stefanofinetti/MF_fcu_efis_mainboard/STL Files/PushPullBlackFlipper.stl

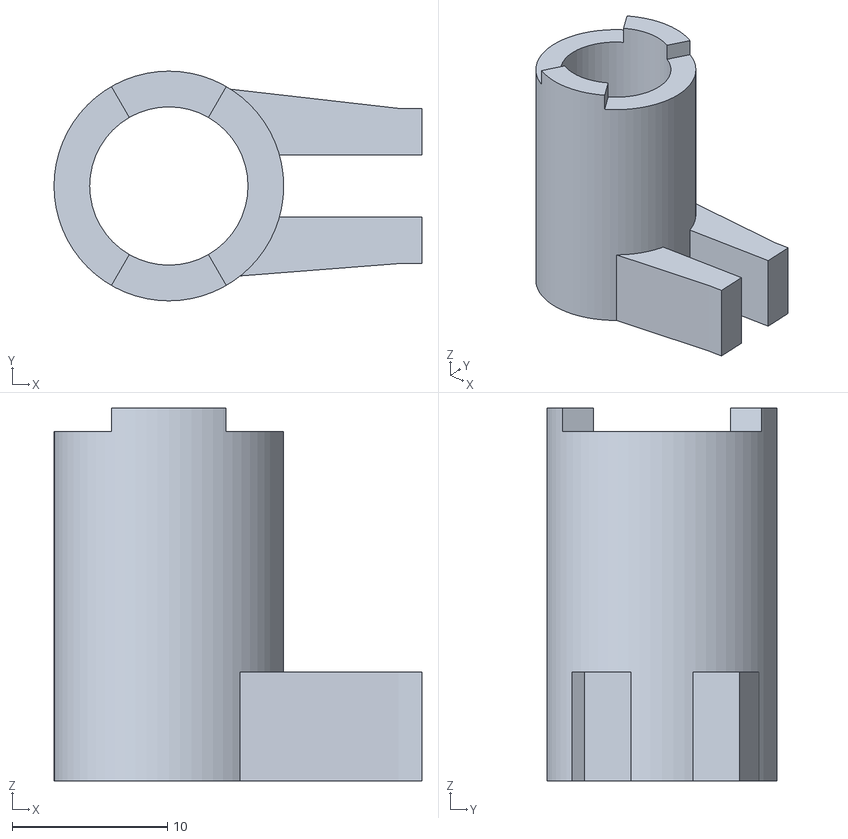
[picture p17: CAD file, 2026-09-20]
STL Files/PushPullBlackFlipper.stl
23.7 x 14.8 x 24.0
