stefanofinetti/MF_fcu_efis_mainboard/STL Files/Rotaries/VSpeedKnob_Base.stl

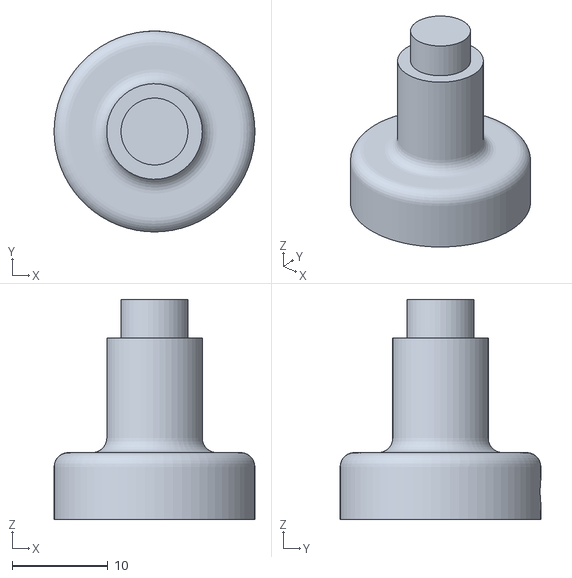
[picture p18: CAD file, 2026-09-20]
STL Files/Rotaries/VSpeedKnob_Base.stl
21.0 x 21.0 x 23.0
