stefanofinetti/MF_fcu_efis_mainboard/STL Files/V4C/FCU_LEFT.3mf

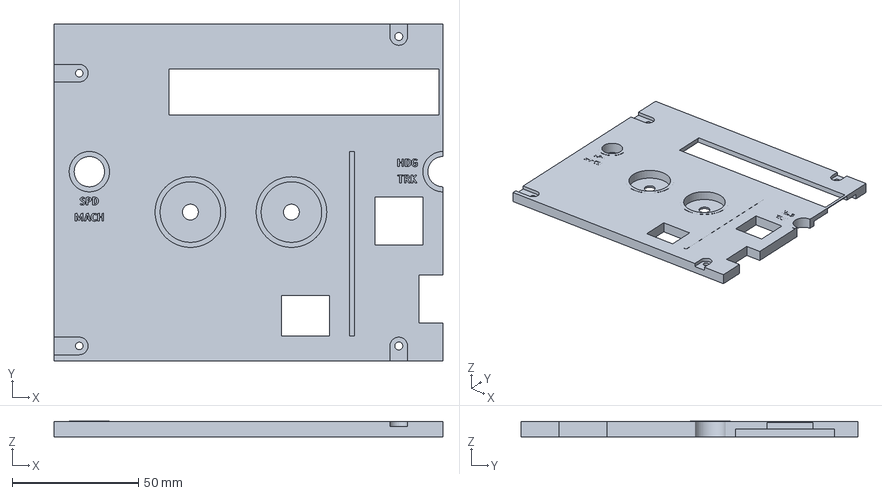
[picture p19: CAD file, 2025-02-01]
STL Files/V4C/FCU_LEFT.3mf
154.0 x 133.5 x 6.18 mm
