stefanofinetti/MF_fcu_efis_mainboard/PSU/3dmodels/Fuse_Bourns_MF-RHT200.step

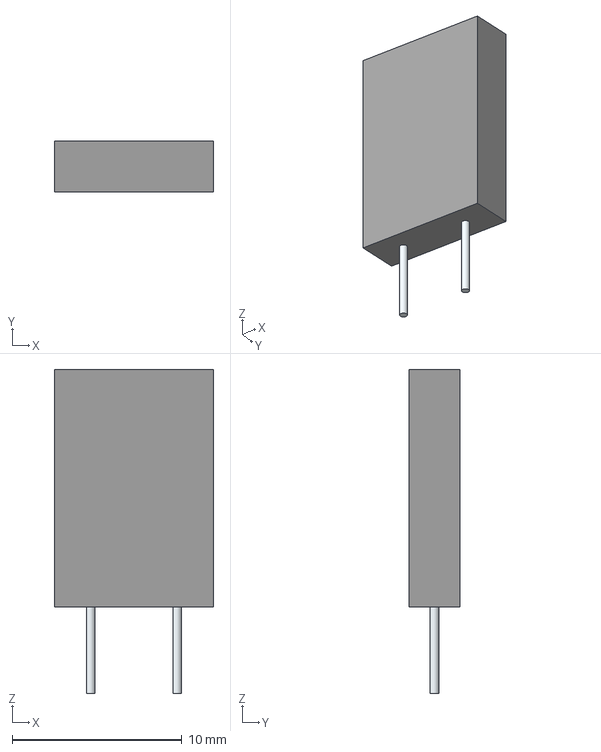
[picture p20: CAD file, 2026-09-22]
PSU/3dmodels/Fuse_Bourns_MF-RHT200.step
9.40 x 3.00 x 19.1 mm
Leads
