stefanofinetti/MF_fcu_efis_mainboard/STL Files/Black/EFIS_FRAME_RIGHT.stl

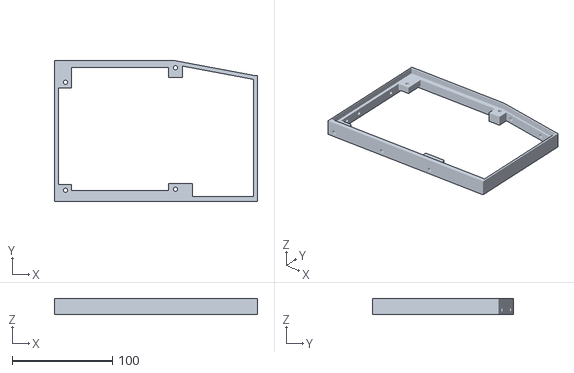
[picture p21: CAD file, 2026-09-20]
STL Files/Black/EFIS_FRAME_RIGHT.stl
203.0 x 140.5 x 16.0
