stefanofinetti/MF_fcu_efis_mainboard/STL Files/FCU_UNIT_V5.3mf

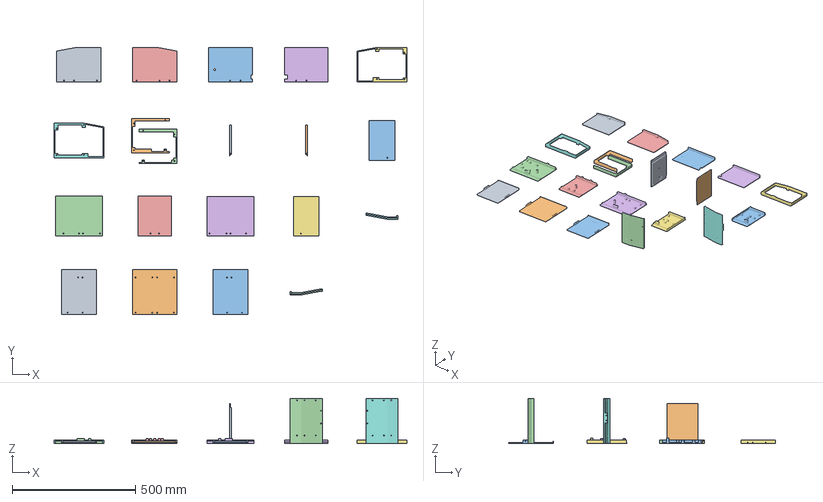
[picture p22: CAD file, 2026-09-20]
STL Files/FCU_UNIT_V5.3mf
1430.8 x 1083.8 x 184.0 mm
EFIS_BACK_LEFT.stl
FCU_FRAME_LEFT.stl
FCU_BACK_LEFT.stl
FCU_FRAME_RIGHT.stl
EFIS_BACK_RIGHT.stl
FCU_BACK_RIGHT.stl
EFIS_FRAME_LEFT.stl
EFIS_FRAME_RIGHT.stl
UNIT_LEFT.stl
UNIT_RIGHT.stl
UNIT_BOTTOM_LEFT.stl
UNIT_BOTTOM_CENTER_LEFT.stl
UNIT_BOTTOM_CENTER.stl
UNIT_BOTTOM_CENTER_RIGHT.stl
UNIT_BOTTOM_RIGHT.stl
UNIT_TOP_LEFT.stl
UNIT_TOP_CENTER_LEFT.stl
UNIT_TOP_CENTER.stl
UNIT_TOP_CENTER_RIGHT.stl
UNIT_TOP_RIGHT.stl
