stefanofinetti/MF_fcu_efis_mainboard/STL Files/Korry_19x16/Korry19_16_project_V5.3mf

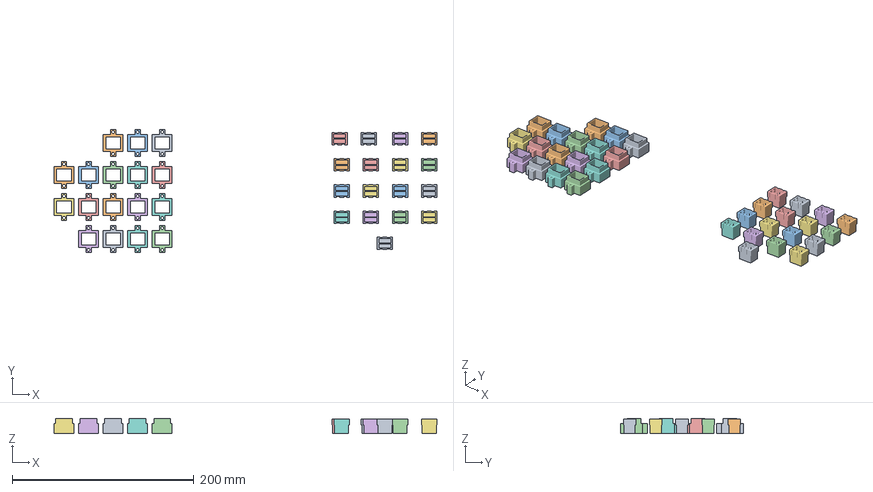
[picture p23: CAD file, 2025-06-19]
STL Files/Korry_19x16/Korry19_16_project_V5.3mf
421.2 x 135.8 x 17.0 mm
Korry19x16_case_v5.stl x 17
APPR_BLACK
ARPT_BLACK x 2
FD_BLACK x 2
CSTR_BLACK x 2
LS_BLACK x 2
NDB_BLACK x 2
VORD_BLACK x 2
WPT_BLACK x 2
EXPD_BLACK
LOC_BLACK
