stefanofinetti/MF_fcu_efis_mainboard/STL Files/Korry_19x19/AT_button.stl

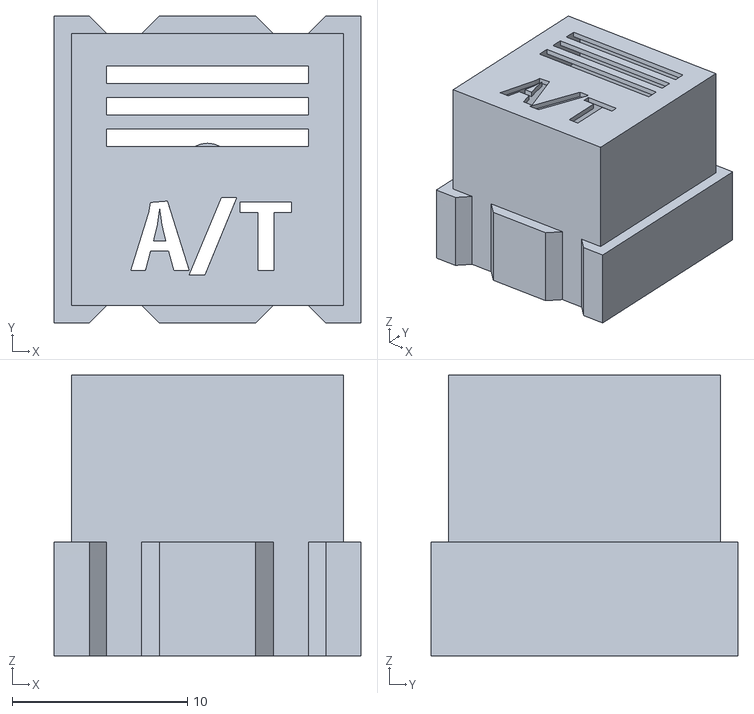
[picture p25: CAD file, 2026-09-20]
STL Files/Korry_19x19/AT_button.stl
17.5 x 17.5 x 16.0
