stefanofinetti/MF_fcu_efis_mainboard/STL Files/Rotaries/PushPull_VSPD_SPD_HDG_case.3mf

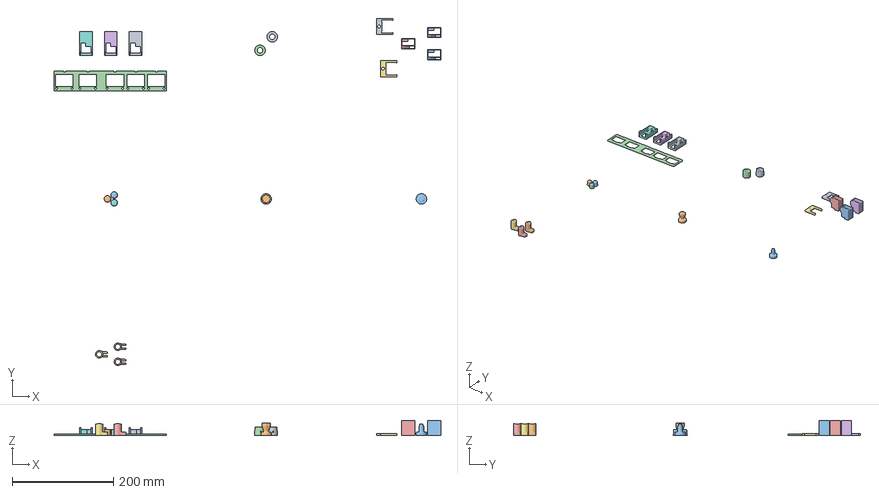
[picture p26: CAD file, 2026-09-20]
STL Files/Rotaries/PushPull_VSPD_SPD_HDG_case.3mf
765.2 x 686.4 x 30.0 mm
PushPullBlackSelector.stl x 2
PushPullBlackFlipper.stl x 3
FCU_BlackButtons_Button x 3
PushPull_ALT_SPD_HDG_cables_case.stl x 3
PushPull_ALT_SPD_HDG_mech_case.stl x 3
FCU_V4_OLED_MASK_V4.stl
PushPullBlackSwitchHolder.stl x 2
HeadingKnob.stl
VSpeedKnob_Base.stl
