stefanofinetti/MF_fcu_efis_mainboard/STL Files/FCU_BlackButtons_TransparentBase.stl

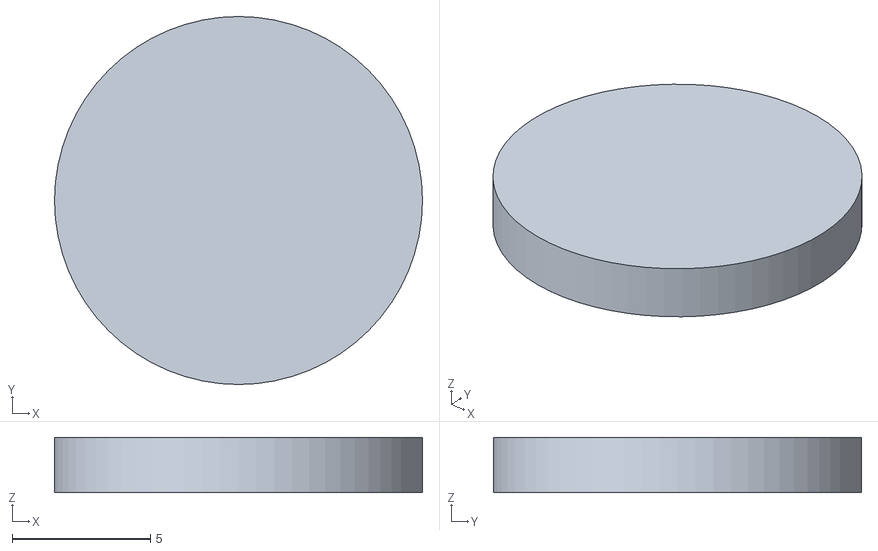
[picture p27: CAD file, 2025-06-21]
STL Files/FCU_BlackButtons_TransparentBase.stl
13.3 x 13.3 x 2.00
