stefanofinetti/MF_fcu_efis_mainboard/STL Files/Korry_19x16/TEST_REVERSED_NDB.stl

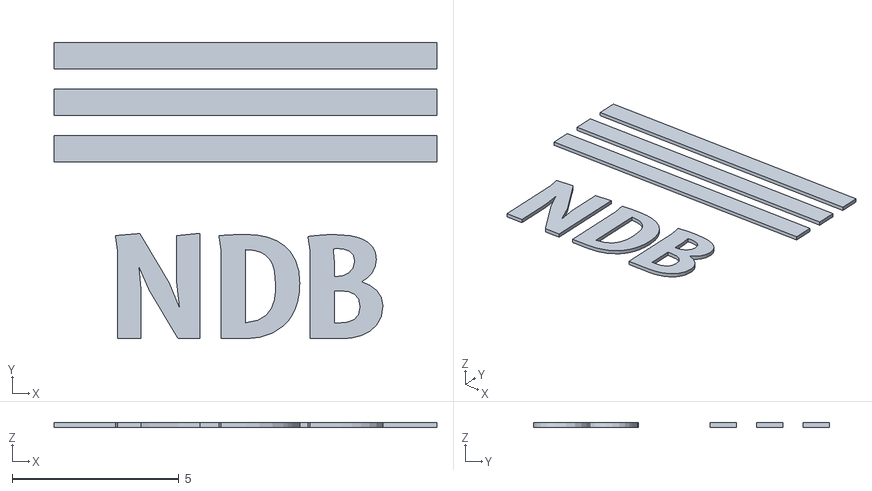
[picture p28: CAD file, 2025-06-19]
STL Files/Korry_19x16/TEST_REVERSED_NDB.stl
11.5 x 8.90 x 0.14
