stefanofinetti/MF_fcu_efis_mainboard/STL Files/Rotaries/PushPullBlackSelector.3mf

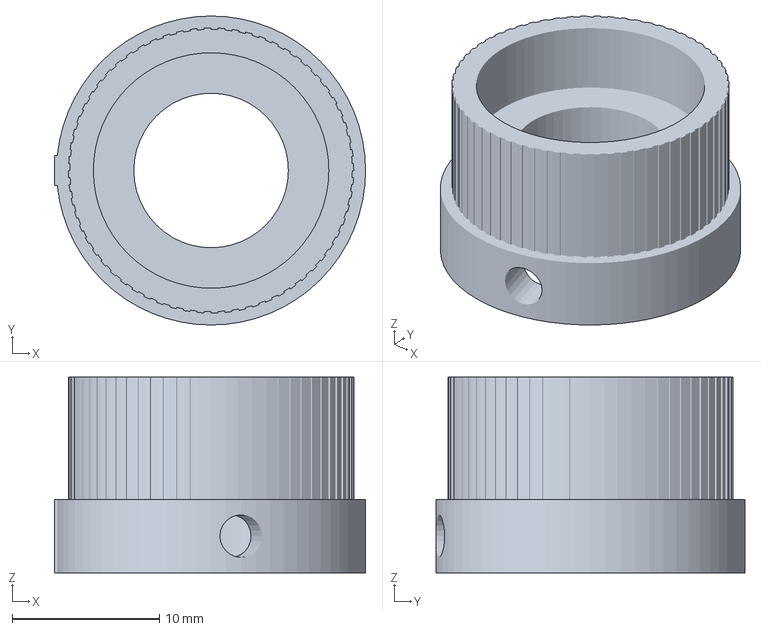
[picture p30: CAD file, 2026-09-20]
STL Files/Rotaries/PushPullBlackSelector.3mf
21.1 x 21.0 x 13.3 mm
