stefanofinetti/MF_fcu_efis_mainboard/STL Files/V4C/FCU_LEFT_TRASP.stl

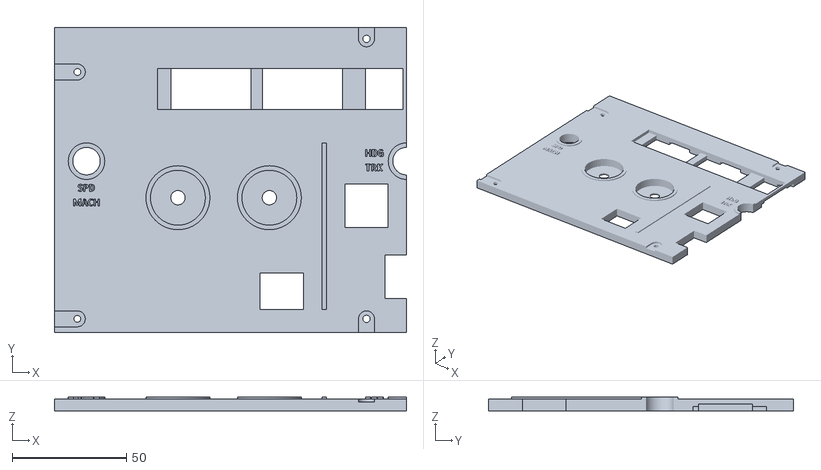
[picture p31: CAD file, 2025-02-01]
STL Files/V4C/FCU_LEFT_TRASP.stl
154.0 x 133.5 x 6.04
