stefanofinetti/MF_fcu_efis_mainboard/STL Files/01_EFIS_V4b_LEFT_firstlayer_transparent.stl

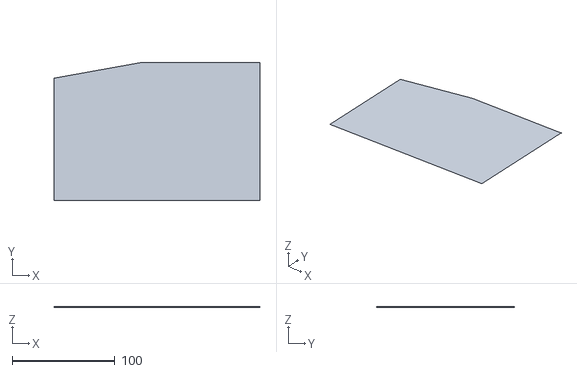
[picture p32: CAD file, 2025-06-21]
STL Files/01_EFIS_V4b_LEFT_firstlayer_transparent.stl
200.0 x 133.5 x 0.1
