stefanofinetti/MF_fcu_efis_mainboard/STL Files/Black/EFIS_BACK_LEFT.stl

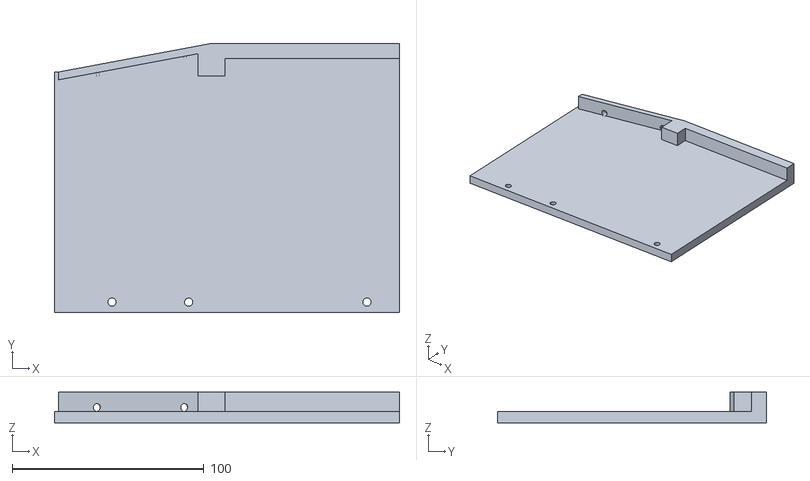
[picture p33: CAD file, 2025-06-19]
STL Files/Black/EFIS_BACK_LEFT.stl
180.0 x 140.5 x 16.0
