stefanofinetti/MF_fcu_efis_mainboard/STL Files/Rotaries/HeadingKnob.stl

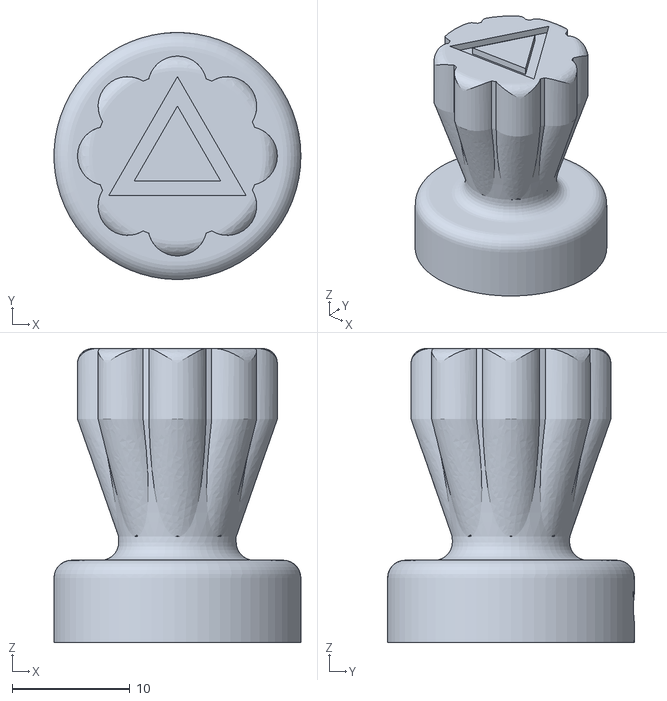
[picture p35: CAD file, 2026-09-20]
STL Files/Rotaries/HeadingKnob.stl
21.0 x 21.0 x 25.0
