stefanofinetti/MF_fcu_efis_mainboard/STL Files/V4C/FCU_RIGHT_GREY.stl

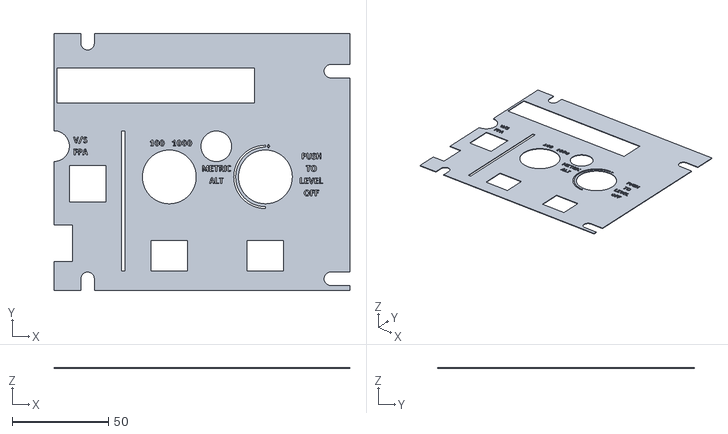
[picture p36: CAD file, 2025-02-01]
STL Files/V4C/FCU_RIGHT_GREY.stl
154.0 x 133.5 x 0.437
