stefanofinetti/MF_fcu_efis_mainboard/STL Files/Black/UNIT_TOP_CENTER_LEFT.stl

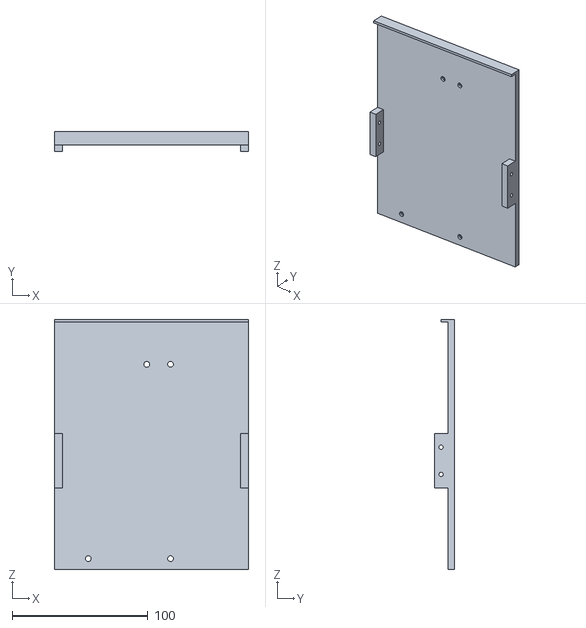
[picture p37: CAD file, 2025-06-19]
STL Files/Black/UNIT_TOP_CENTER_LEFT.stl
143.0 x 15.0 x 184.0
