stefanofinetti/MF_fcu_efis_mainboard/STL Files/FCU_BlackButtons_Button.stl

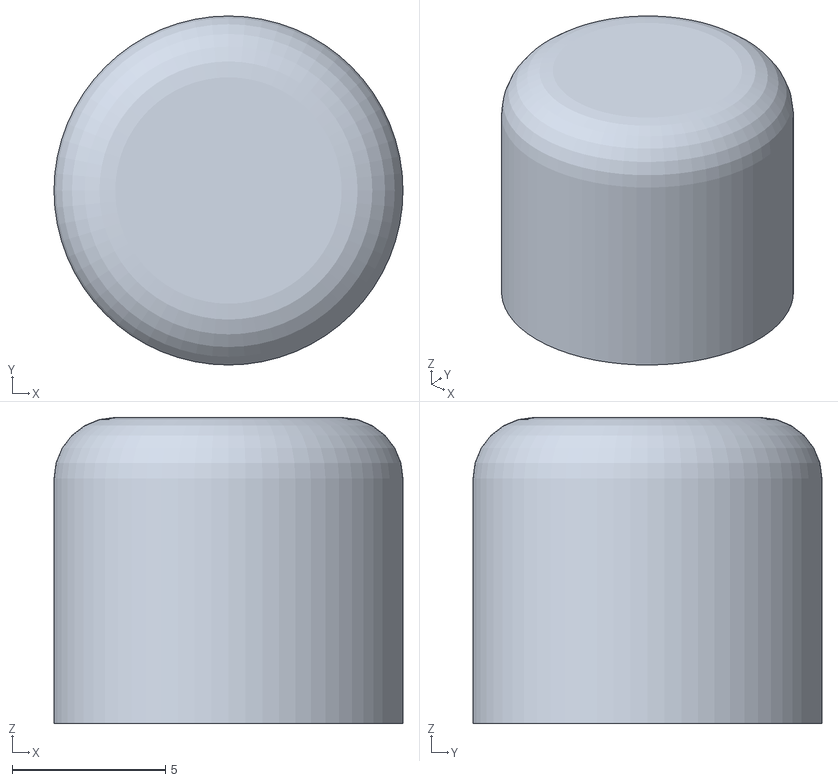
[picture p38: CAD file, 2025-06-21]
STL Files/FCU_BlackButtons_Button.stl
11.4 x 11.4 x 10.0
