stefanofinetti/MF_fcu_efis_mainboard/STL Files/Korry_19x16/V5/WPT_TRASP.stl

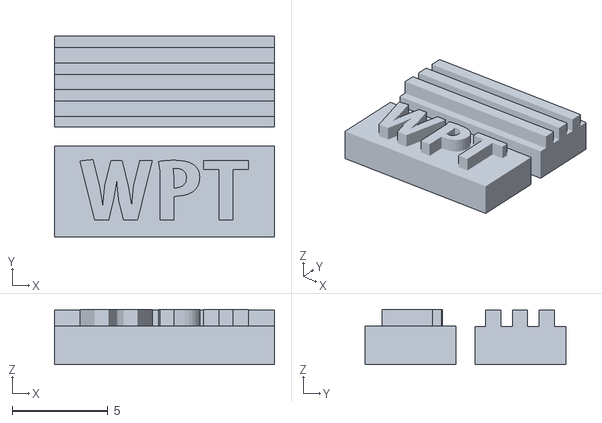
[picture p39: CAD file, 2025-06-19]
STL Files/Korry_19x16/V5/WPT_TRASP.stl
11.5 x 10.5 x 2.88
