stefanofinetti/MF_fcu_efis_mainboard/STL Files/Korry_19x19/AT_transparent.stl

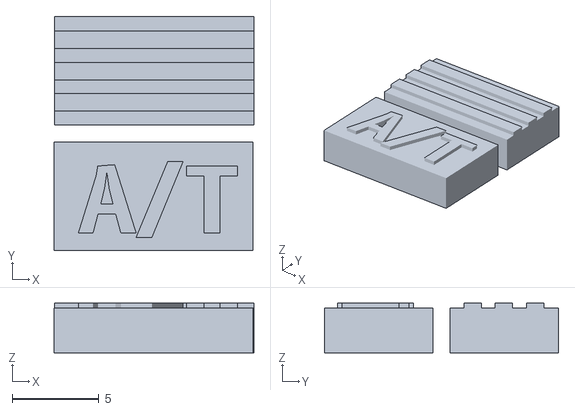
[picture p40: CAD file, 2025-06-21]
STL Files/Korry_19x19/AT_transparent.stl
11.5 x 13.5 x 2.86
