stefanofinetti/MF_fcu_efis_mainboard/STL Files/Rotaries/Rotary_ALT_BARO_Outer_case.stl

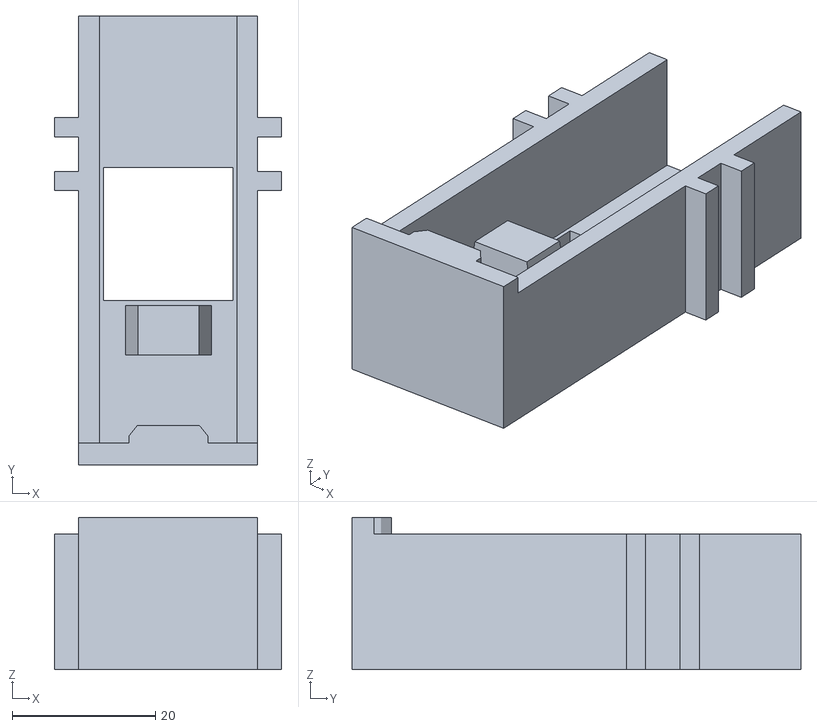
[picture p41: CAD file, 2026-09-20]
STL Files/Rotaries/Rotary_ALT_BARO_Outer_case.stl
31.7 x 62.6 x 21.2
