stefanofinetti/MF_fcu_efis_mainboard/STL Files/Korry_19x16/LS_white.stl

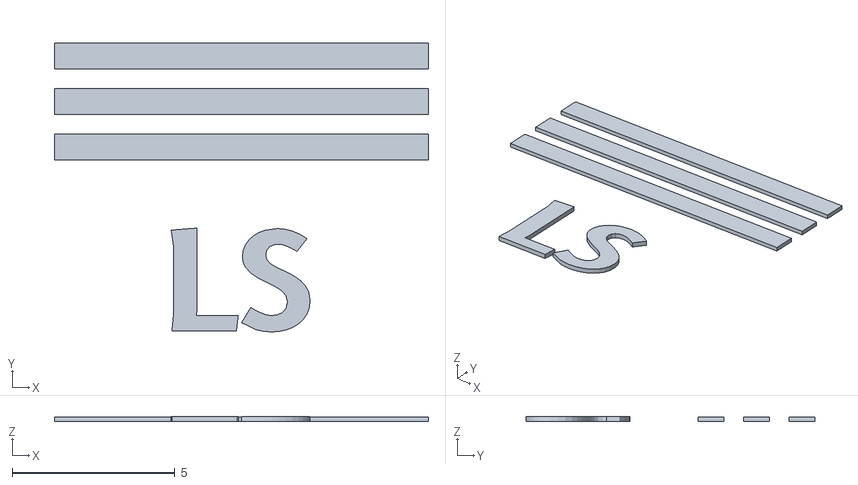
[picture p42: CAD file, 2024-11-27]
STL Files/Korry_19x16/LS_white.stl
11.5 x 8.88 x 0.16
