stefanofinetti/MF_fcu_efis_mainboard/STL Files/Rotaries/PushPull_VSPD_SPD_HDG_cables_case.stl

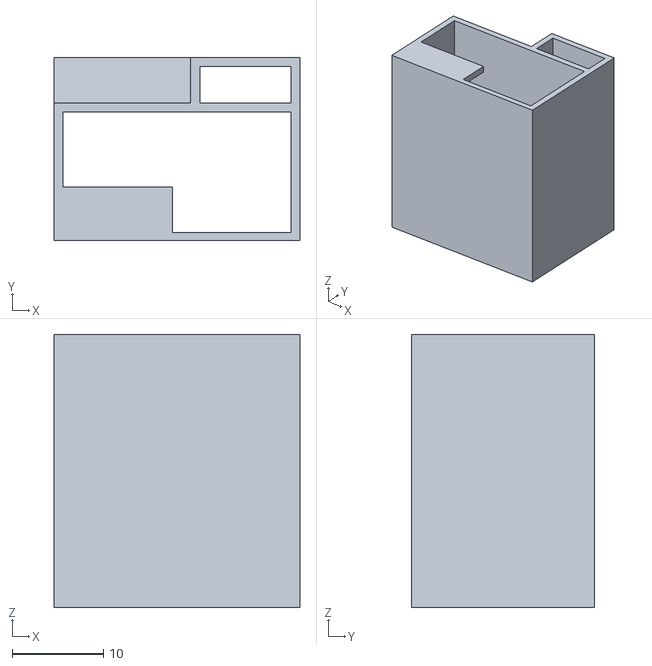
[picture p44: CAD file, 2025-06-19]
STL Files/Rotaries/PushPull_VSPD_SPD_HDG_cables_case.stl
27.0 x 20.1 x 30.0
