stefanofinetti/MF_fcu_efis_mainboard/STL Files/EVIS_V4b_Backlighting_Support.stl

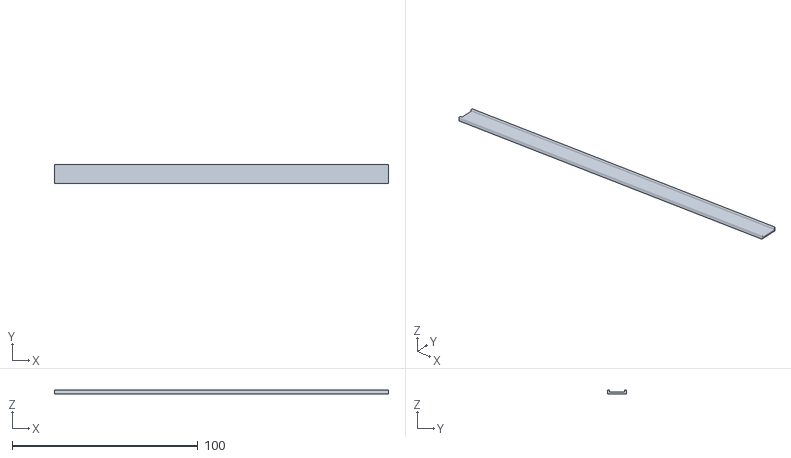
[picture p45: CAD file, 2025-06-19]
STL Files/EVIS_V4b_Backlighting_Support.stl
180.0 x 10.0 x 2.00
