stefanofinetti/MF_fcu_efis_mainboard/STL Files/Korry_19x19/AP2_white.stl

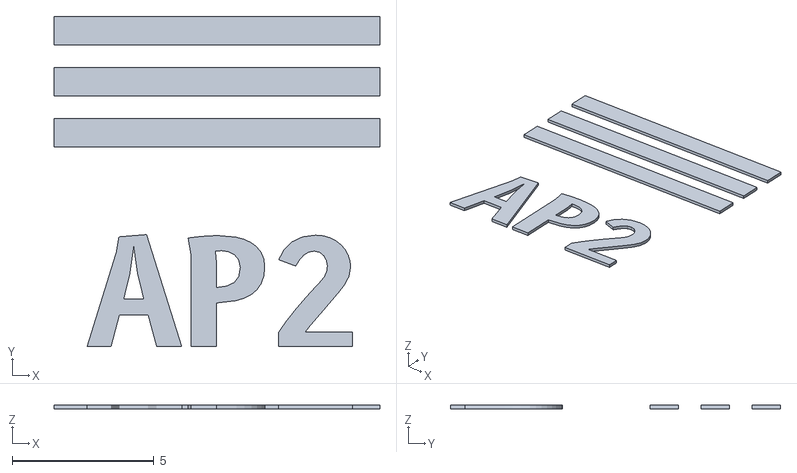
[picture p47: CAD file, 2025-06-21]
STL Files/Korry_19x19/AP2_white.stl
11.5 x 11.7 x 0.14
