stefanofinetti/MF_fcu_efis_mainboard/STL Files/Rotaries/PushPullBlackSwitchHolder.stl

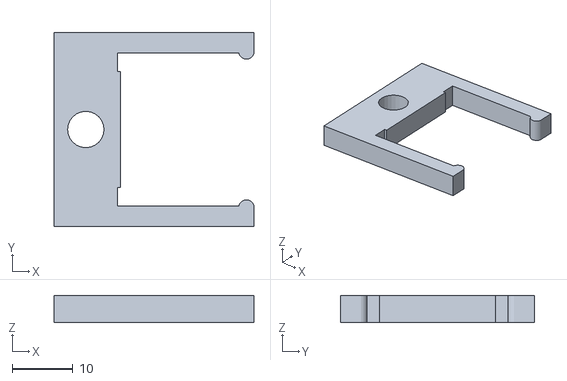
[picture p48: CAD file, 2025-06-19]
STL Files/Rotaries/PushPullBlackSwitchHolder.stl
33.0 x 32.0 x 4.50
