stefanofinetti/MF_fcu_efis_mainboard/STL Files/V4C/FCU_RIGHT_WHITE.stl

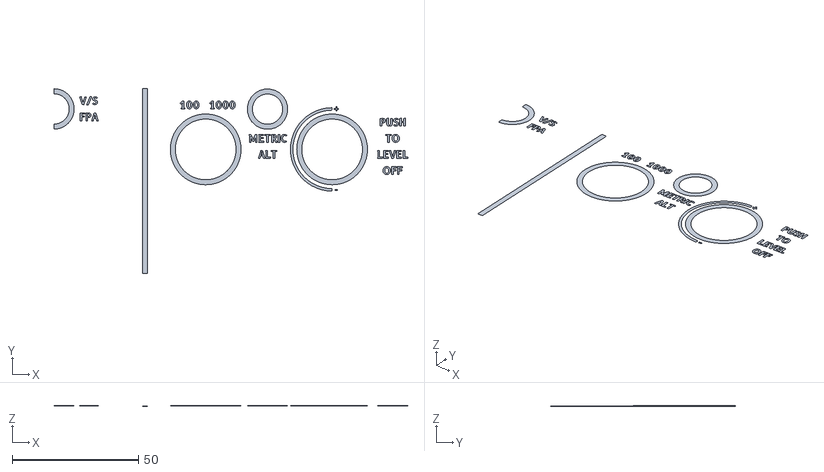
[picture p49: CAD file, 2025-02-01]
STL Files/V4C/FCU_RIGHT_WHITE.stl
140.0 x 73.0 x 0.22
