stefanofinetti/MF_fcu_efis_mainboard/STL Files/05_FCU_V4b_RIGHT_RAILS_white.stl

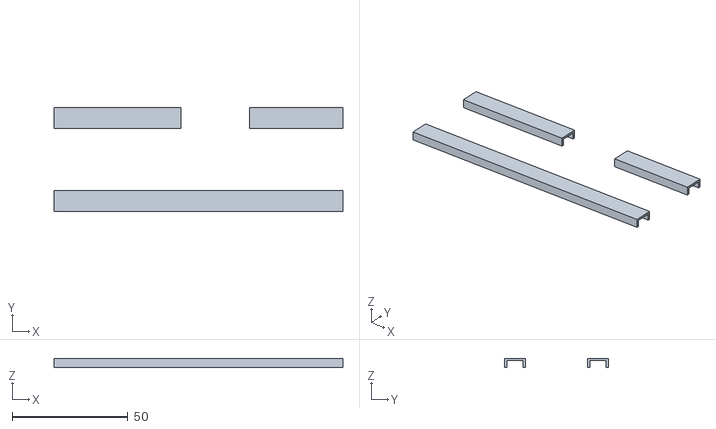
[picture p50: CAD file, 2025-06-19]
STL Files/05_FCU_V4b_RIGHT_RAILS_white.stl
125.0 x 45.0 x 4.00
