stefanofinetti/MF_fcu_efis_mainboard/STL Files/Black/UNIT_TOP_LEFT.stl

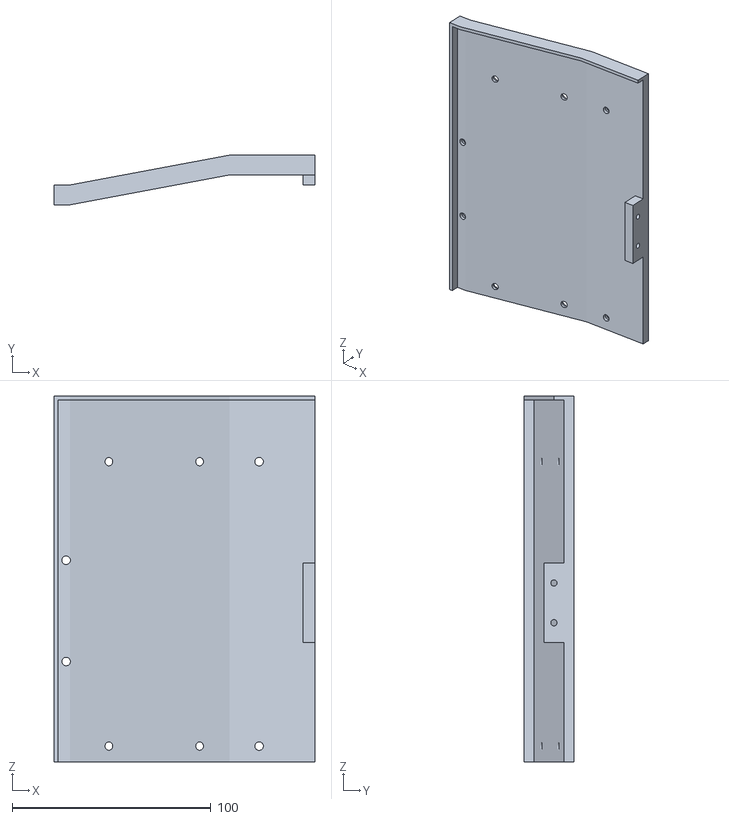
[picture p51: CAD file, 2025-06-19]
STL Files/Black/UNIT_TOP_LEFT.stl
131.0 x 25.0 x 184.0
