stefanofinetti/MF_fcu_efis_mainboard/STL Files/Rotaries/PushPull_VSPD_SPD_HDG_mech_case.stl

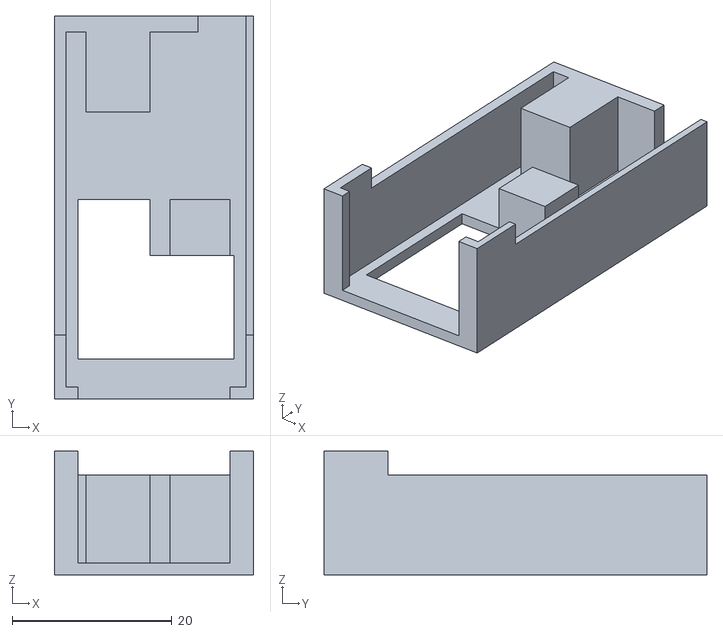
[picture p53: CAD file, 2025-06-19]
STL Files/Rotaries/PushPull_VSPD_SPD_HDG_mech_case.stl
25.0 x 48.0 x 15.5
