stefanofinetti/MF_fcu_efis_mainboard/STL Files/V4C/FCU_LEFT_WHITE.stl

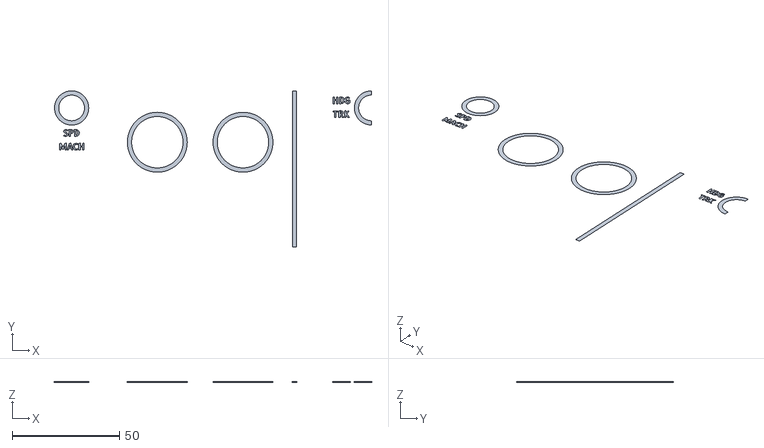
[picture p54: CAD file, 2025-02-01]
STL Files/V4C/FCU_LEFT_WHITE.stl
148.0 x 73.0 x 0.18
