stefanofinetti/MF_fcu_efis_mainboard/STL Files/Black/UNIT_BOTTOM_CENTER_RIGHT.stl

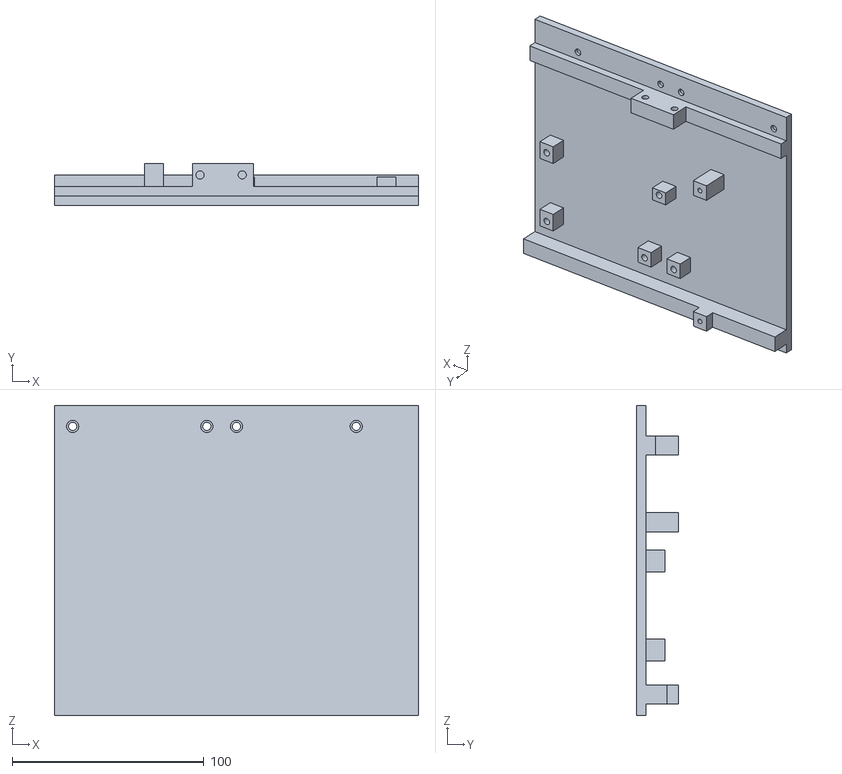
[picture p55: CAD file, 2025-06-19]
STL Files/Black/UNIT_BOTTOM_CENTER_RIGHT.stl
190.0 x 22.0 x 162.0
