stefanofinetti/MF_fcu_efis_mainboard/STL Files/EFIS_LEFT_LED_RAILS_COVER.stl

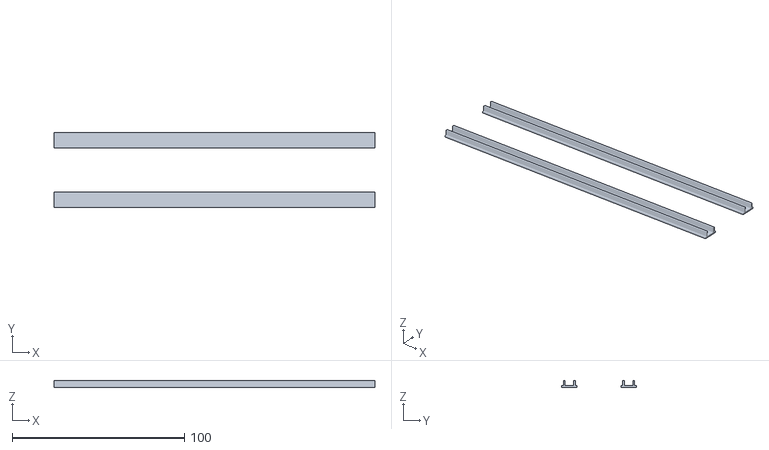
[picture p56: CAD file, 2025-06-19]
STL Files/EFIS_LEFT_LED_RAILS_COVER.stl
186.5 x 43.5 x 4.00
