stefanofinetti/MF_fcu_efis_mainboard/STL Files/Rotaries/Atl-Baro-100-100-Switch_Long.stl

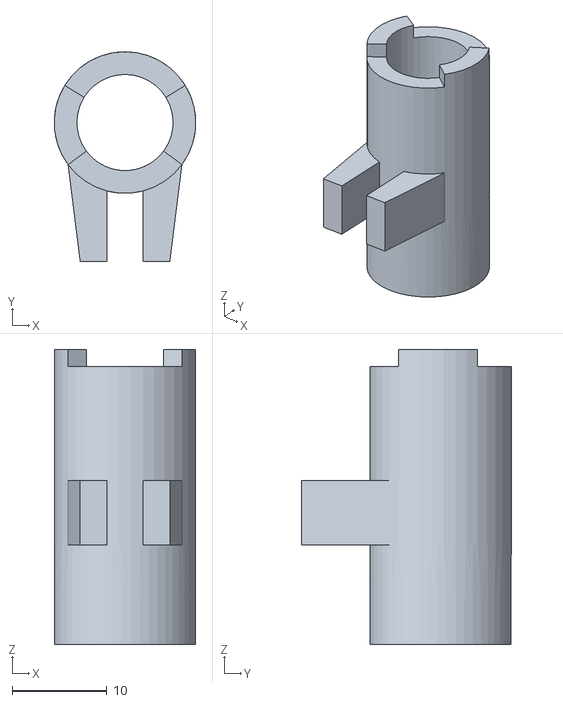
[picture p58: CAD file, 2025-02-01]
STL Files/Rotaries/Atl-Baro-100-100-Switch_Long.stl
14.9 x 22.1 x 31.2
