stefanofinetti/MF_fcu_efis_mainboard/STL Files/Black/UNIT_BOTTOM_LEFT.stl

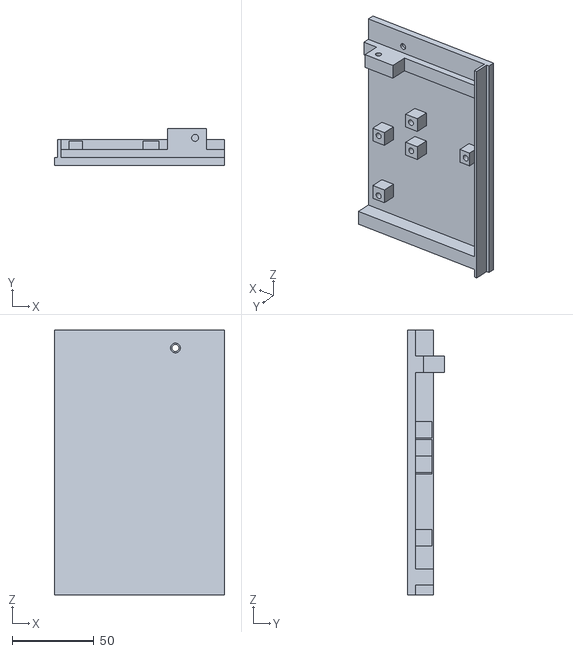
[picture p59: CAD file, 2025-06-19]
STL Files/Black/UNIT_BOTTOM_LEFT.stl
104.0 x 22.8 x 162.0
