stefanofinetti/MF_fcu_efis_mainboard/STL Files/Korry_19x16/EXPD_Button_Black.stl

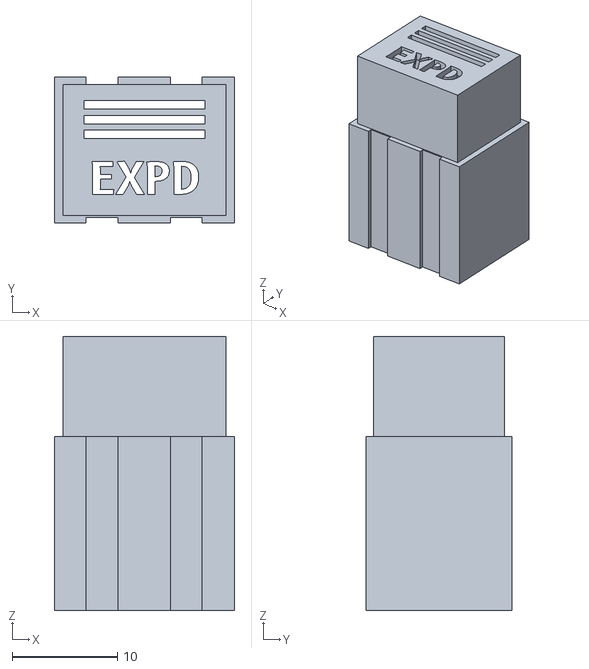
[picture p60: CAD file, 2024-11-27]
STL Files/Korry_19x16/EXPD_Button_Black.stl
17.1 x 13.8 x 26.0
