stefanofinetti/MF_fcu_efis_mainboard/STL Files/Rotaries/Alt-baro-Rotary-ConnectionPanel.stl

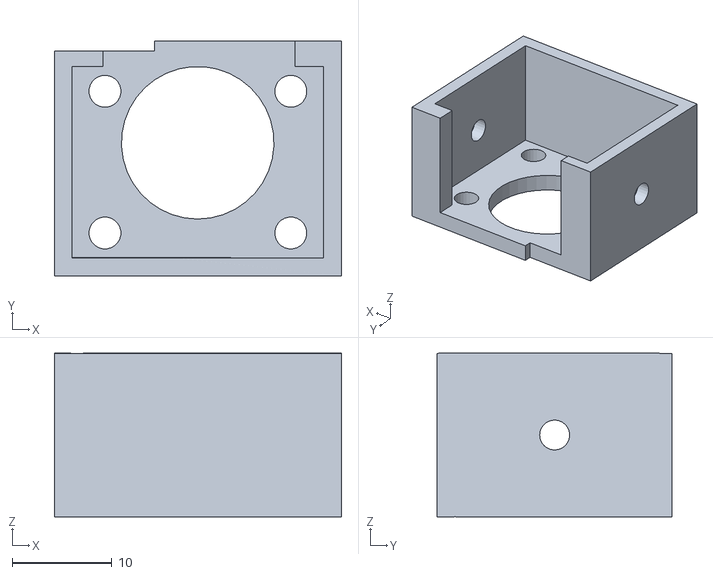
[picture p62: CAD file, 2025-02-01]
STL Files/Rotaries/Alt-baro-Rotary-ConnectionPanel.stl
28.7 x 23.5 x 16.4
