stefanofinetti/MF_fcu_efis_mainboard/STL Files/Black/UNIT_TOP_CENTER.stl

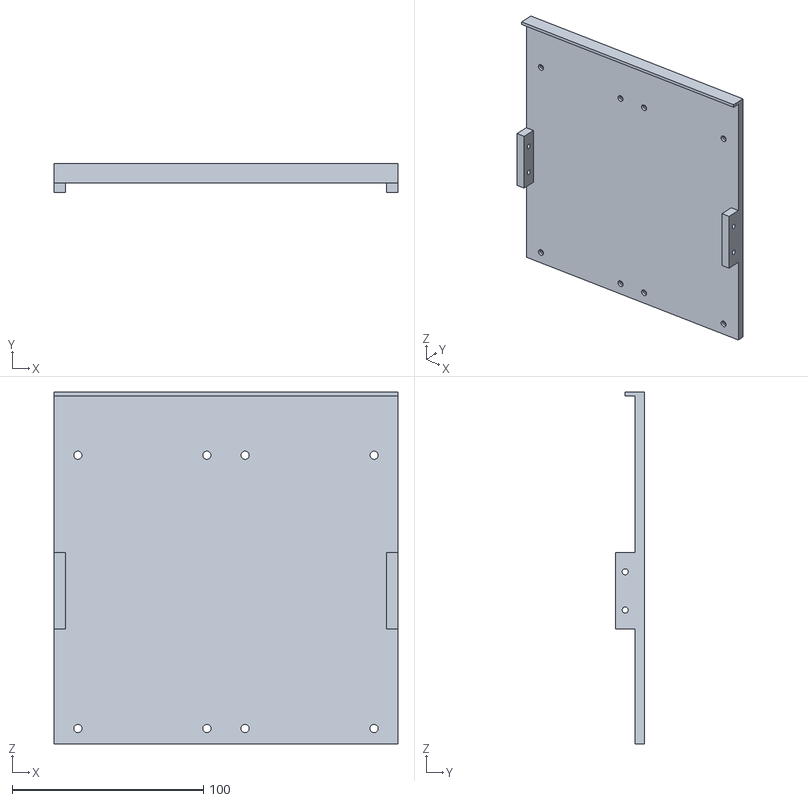
[picture p63: CAD file, 2025-06-19]
STL Files/Black/UNIT_TOP_CENTER.stl
180.0 x 15.0 x 184.0
