stefanofinetti/MF_fcu_efis_mainboard/STL Files/Korry_19x16/ARPT_white.stl

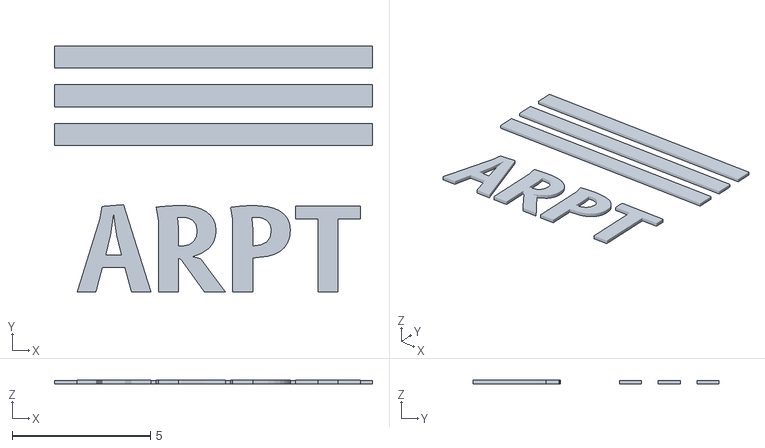
[picture p64: CAD file, 2024-11-27]
STL Files/Korry_19x16/ARPT_white.stl
11.5 x 8.90 x 0.16
