stefanofinetti/MF_fcu_efis_mainboard/STL Files/01_EFIS_LEFT_V4b.3mf

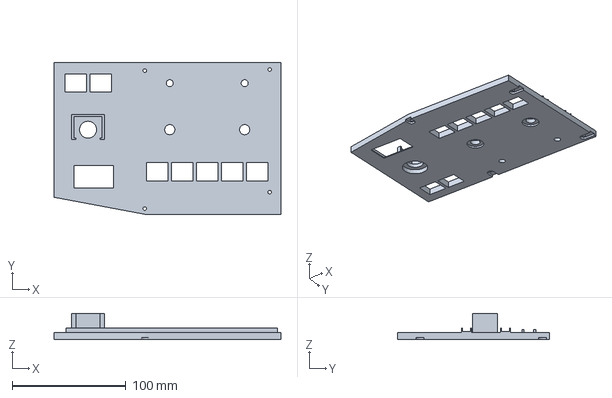
[picture p65: CAD file, 2025-06-19]
STL Files/01_EFIS_LEFT_V4b.3mf
200.0 x 133.5 x 23.0 mm
