stefanofinetti/MF_fcu_efis_mainboard/STL Files/Korry_19x16/WPT_white.stl

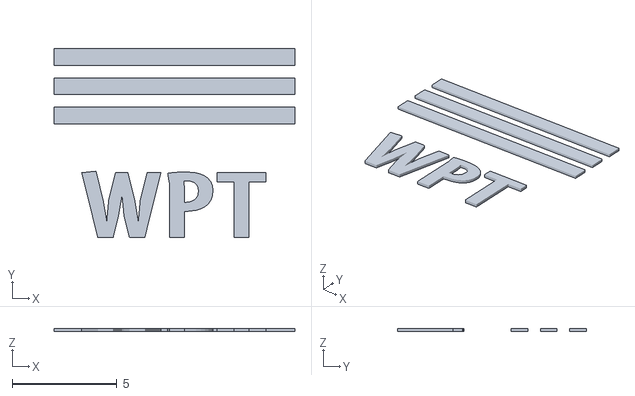
[picture p66: CAD file, 2024-11-27]
STL Files/Korry_19x16/WPT_white.stl
11.5 x 9.02 x 0.16
