stefanofinetti/MF_fcu_efis_mainboard/STL Files/05_FCU_V4b_LEFT_RAILS_white.stl

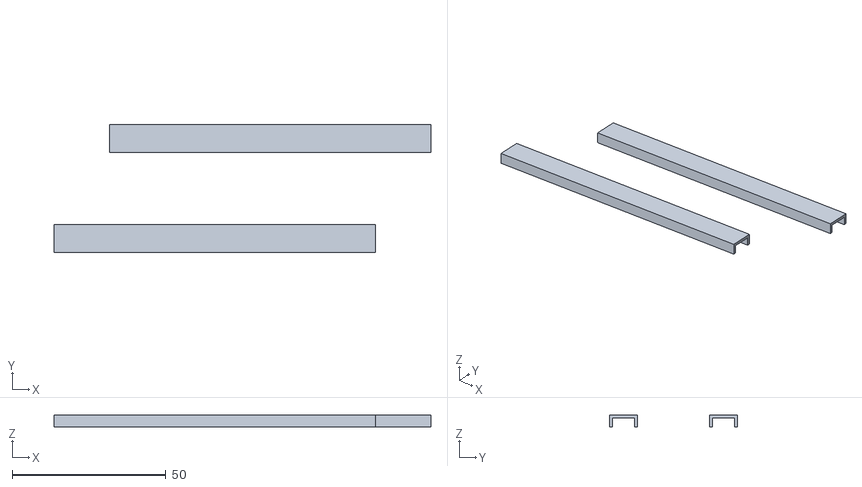
[picture p67: CAD file, 2025-06-19]
STL Files/05_FCU_V4b_LEFT_RAILS_white.stl
122.5 x 41.5 x 4.00
