stefanofinetti/MF_fcu_efis_mainboard/STL Files/Black/UNIT_LEFT.stl

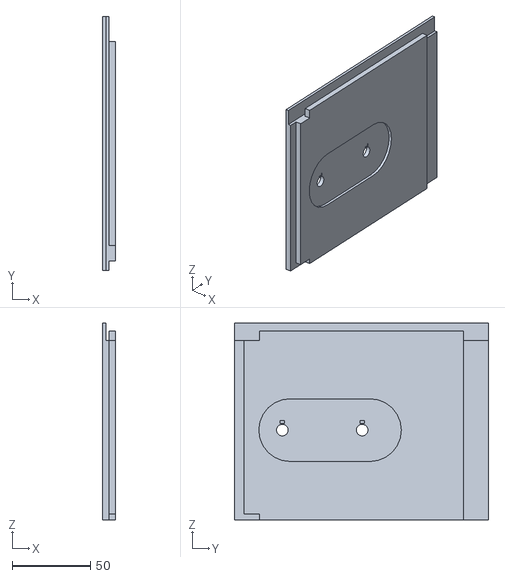
[picture p68: CAD file, 2025-06-19]
STL Files/Black/UNIT_LEFT.stl
8.00 x 162.0 x 125.5
