stefanofinetti/MF_fcu_efis_mainboard/STL Files/04_FCU_V4b_RIGHT_white.stl

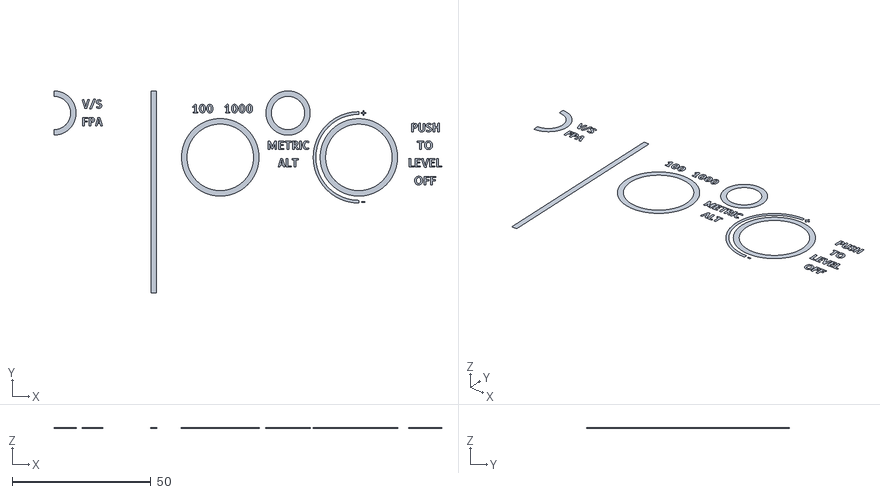
[picture p69: CAD file, 2025-06-19]
STL Files/04_FCU_V4b_RIGHT_white.stl
140.0 x 73.0 x 0.16
