stefanofinetti/MF_fcu_efis_mainboard/STL Files/Black/FCU_BACK_LEFT.stl

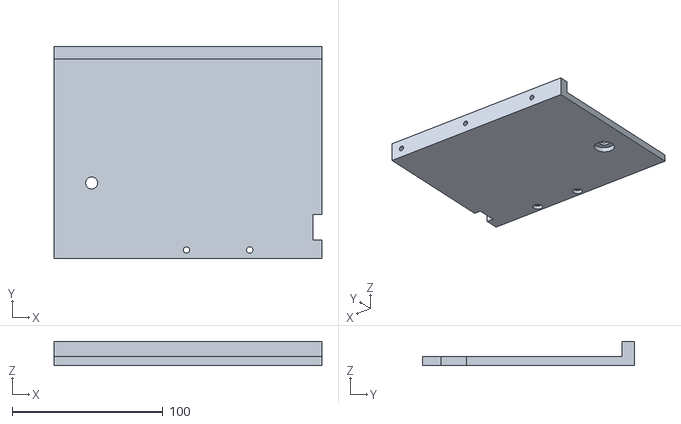
[picture p70: CAD file, 2025-06-19]
STL Files/Black/FCU_BACK_LEFT.stl
178.0 x 140.5 x 16.0
