stefanofinetti/MF_fcu_efis_mainboard/STL Files/Korry_19x16/V5/VORD_WHITE.stl

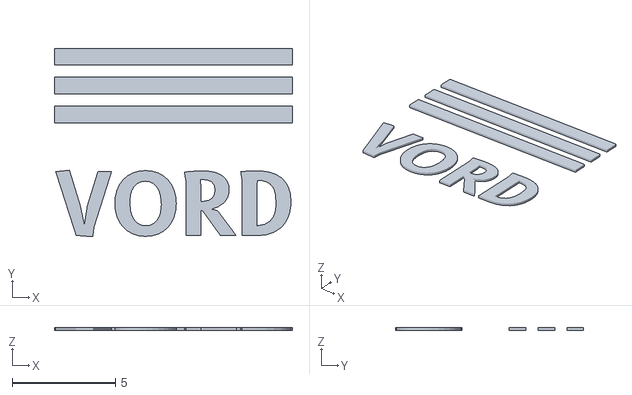
[picture p71: CAD file, 2025-06-19]
STL Files/Korry_19x16/V5/VORD_WHITE.stl
11.5 x 9.11 x 0.14
