stefanofinetti/MF_fcu_efis_mainboard/STL Files/04_EFIS_V4b_LEFT_white.stl

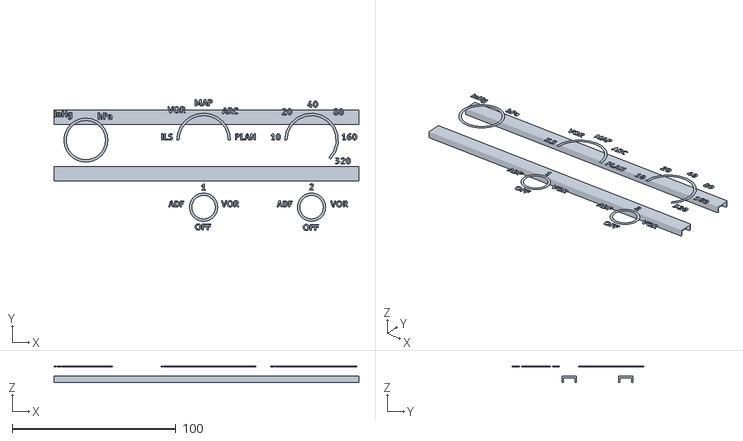
[picture p72: CAD file, 2025-06-19]
STL Files/04_EFIS_V4b_LEFT_white.stl
186.5 x 80.3 x 10.0
