stefanofinetti/MF_fcu_efis_mainboard/STL Files/Korry_19x16/CSTR_white.stl

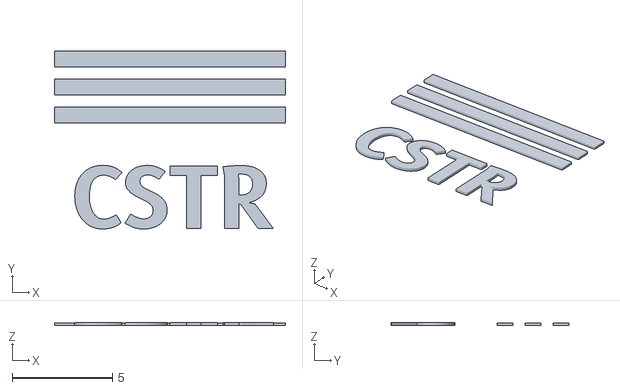
[picture p73: CAD file, 2024-11-27]
STL Files/Korry_19x16/CSTR_white.stl
11.5 x 8.87 x 0.16
