stefanofinetti/MF_fcu_efis_mainboard/STL Files/04_FCU_V4b_LEFT_white.stl

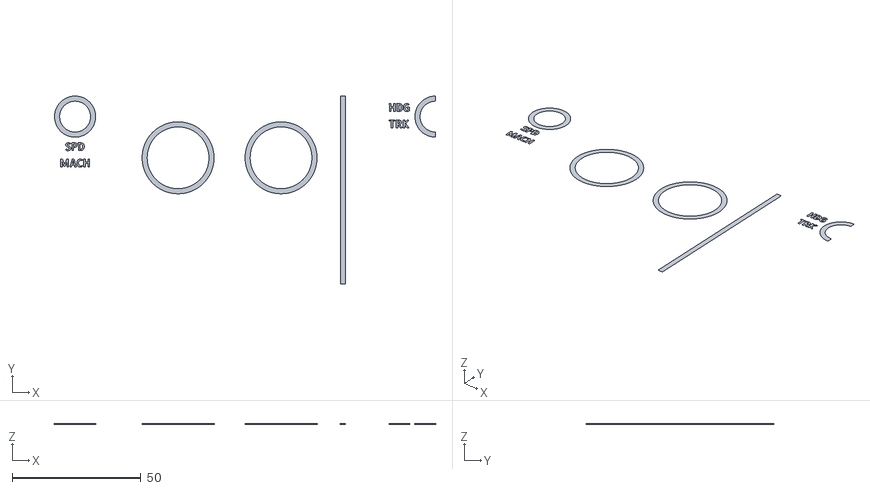
[picture p75: CAD file, 2025-06-19]
STL Files/04_FCU_V4b_LEFT_white.stl
148.0 x 73.0 x 0.14
