stefanofinetti/MF_fcu_efis_mainboard/STL Files/01_FCU_V4b_RIGHT_transparent.stl

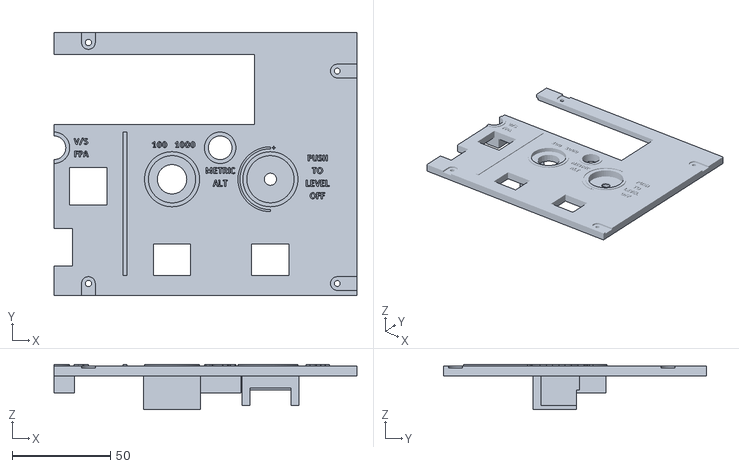
[picture p76: CAD file, 2025-06-19]
STL Files/01_FCU_V4b_RIGHT_transparent.stl
154.0 x 133.5 x 22.9
