stefanofinetti/MF_fcu_efis_mainboard/STL Files/Black/UNIT_BOTTOM_CENTER.stl

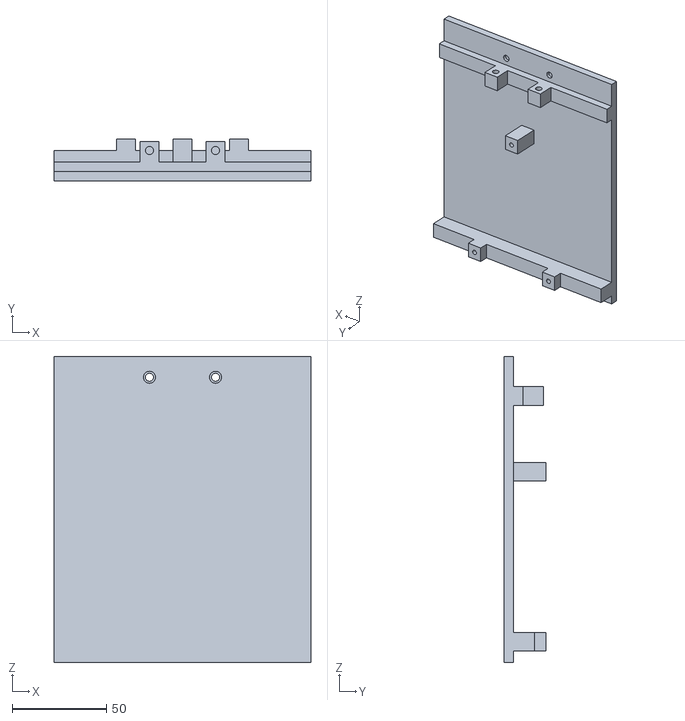
[picture p77: CAD file, 2025-06-19]
STL Files/Black/UNIT_BOTTOM_CENTER.stl
136.0 x 22.0 x 162.0
