stefanofinetti/MF_fcu_efis_mainboard/STL Files/Black/UNIT_RIGHT.stl

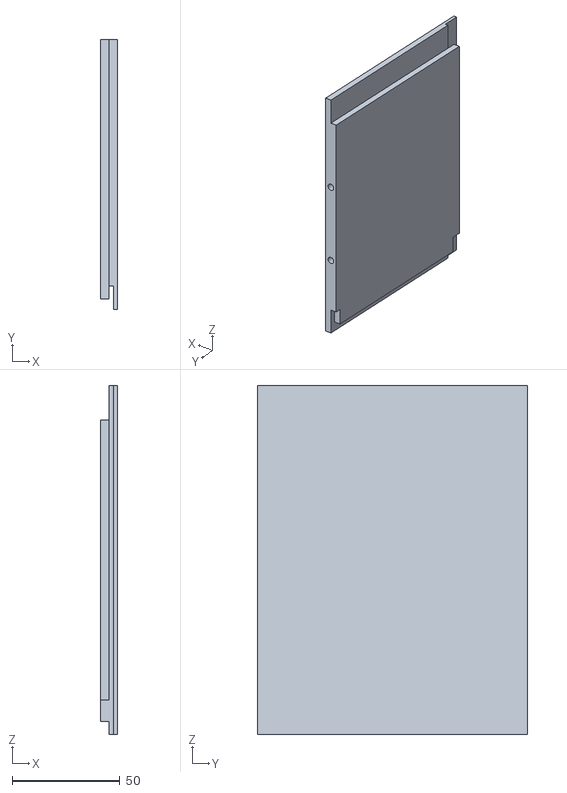
[picture p79: CAD file, 2025-06-19]
STL Files/Black/UNIT_RIGHT.stl
8.00 x 125.5 x 162.0
