stefanofinetti/MF_fcu_efis_mainboard/STL Files/Korry_19x16/LS_transparent.stl

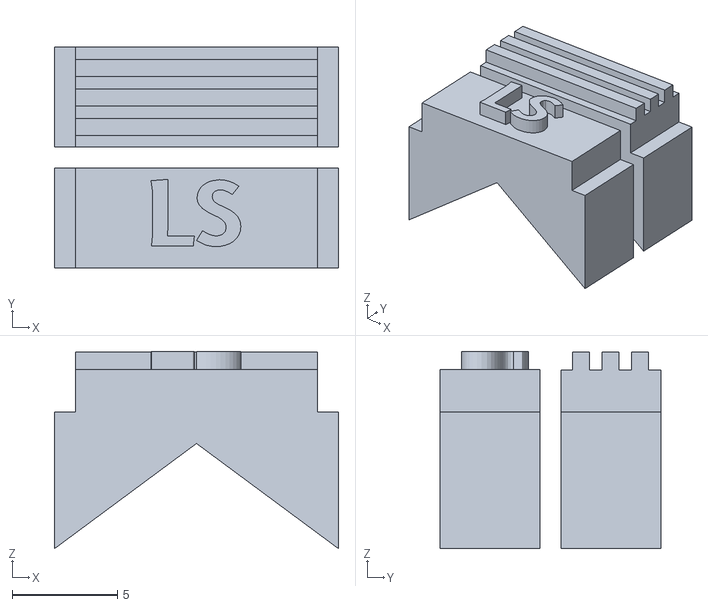
[picture p80: CAD file, 2024-11-27]
STL Files/Korry_19x16/LS_transparent.stl
13.5 x 10.5 x 9.38
