stefanofinetti/MF_fcu_efis_mainboard/STL Files/03_EFIS_V4b_RIGHT_gray.stl

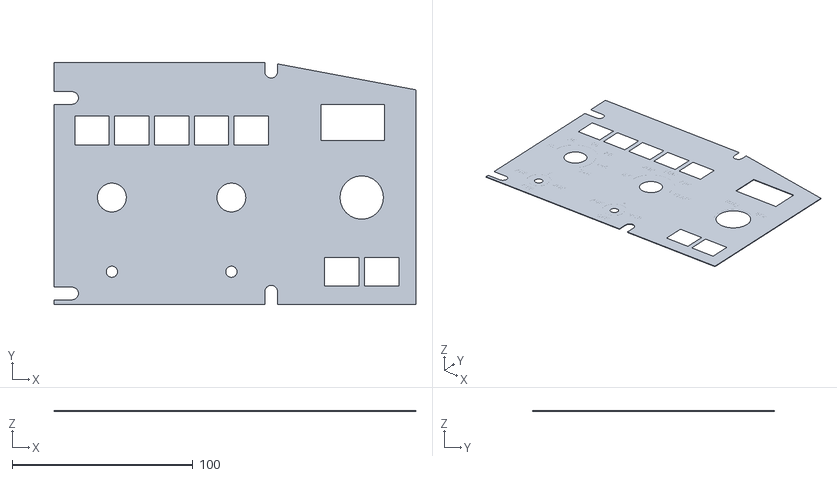
[picture p81: CAD file, 2025-06-19]
STL Files/03_EFIS_V4b_RIGHT_gray.stl
200.0 x 133.5 x 0.42
