stefanofinetti/MF_fcu_efis_mainboard/STL Files/01_EFIS_V4b_LEFT_transparent.stl

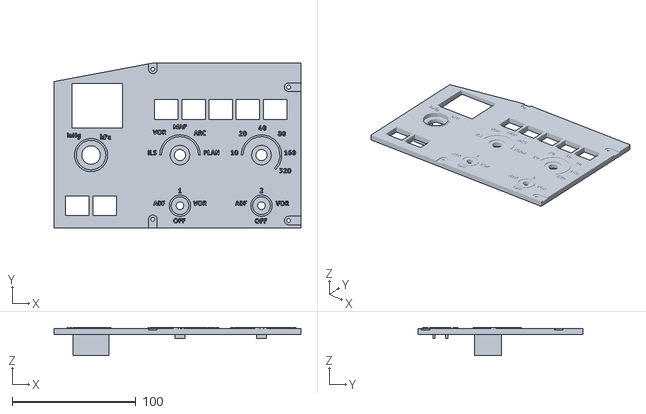
[picture p83: CAD file, 2025-06-19]
STL Files/01_EFIS_V4b_LEFT_transparent.stl
200.0 x 133.5 x 23.0
