stefanofinetti/MF_fcu_efis_mainboard/STL Files/02_EFIS_V4b_LEFT_black.stl

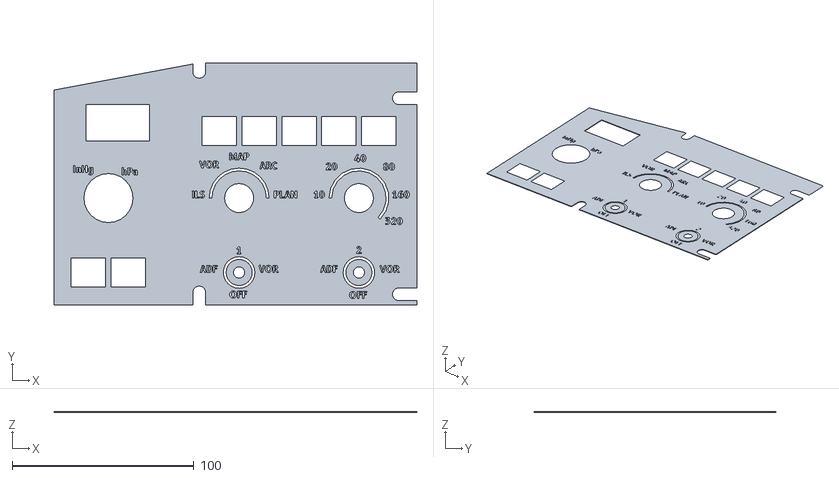
[picture p85: CAD file, 2025-06-19]
STL Files/02_EFIS_V4b_LEFT_black.stl
200.0 x 133.5 x 0.42
