stefanofinetti/MF_fcu_efis_mainboard/STL Files/Korry_19x16/V5/FD_WHITE.stl

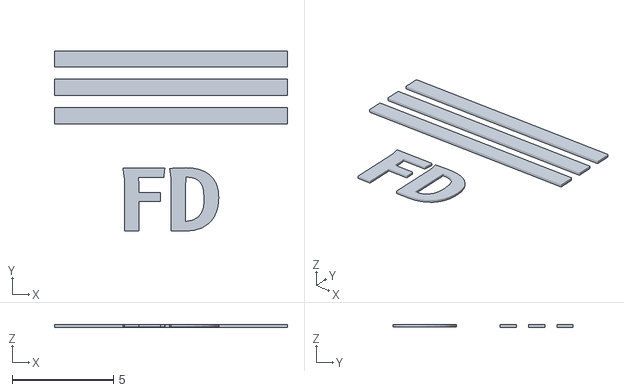
[picture p86: CAD file, 2025-06-19]
STL Files/Korry_19x16/V5/FD_WHITE.stl
11.5 x 8.90 x 0.14
