stefanofinetti/MF_fcu_efis_mainboard/STL Files/04_EFIS_V4b_RIGHT_white.stl

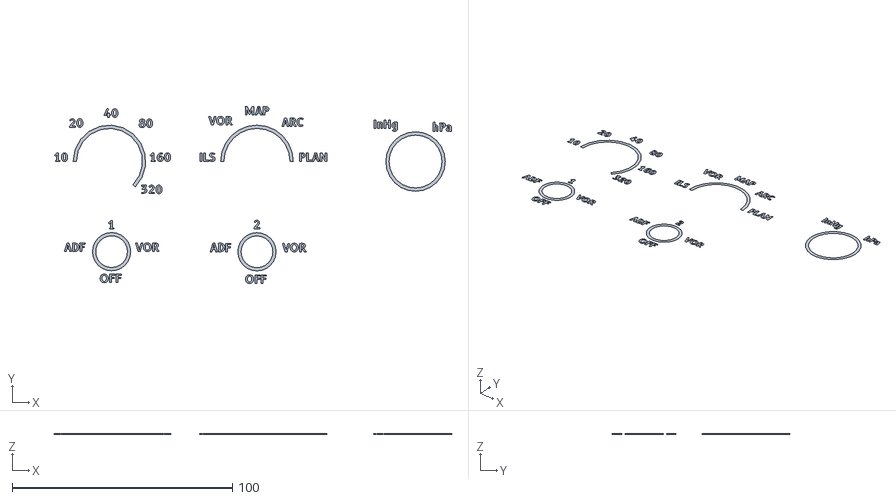
[picture p87: CAD file, 2025-06-19]
STL Files/04_EFIS_V4b_RIGHT_white.stl
180.3 x 80.4 x 0.14
