stefanofinetti/MF_fcu_efis_mainboard/STL Files/01_FCU_V4b_LEFT_transparent.stl

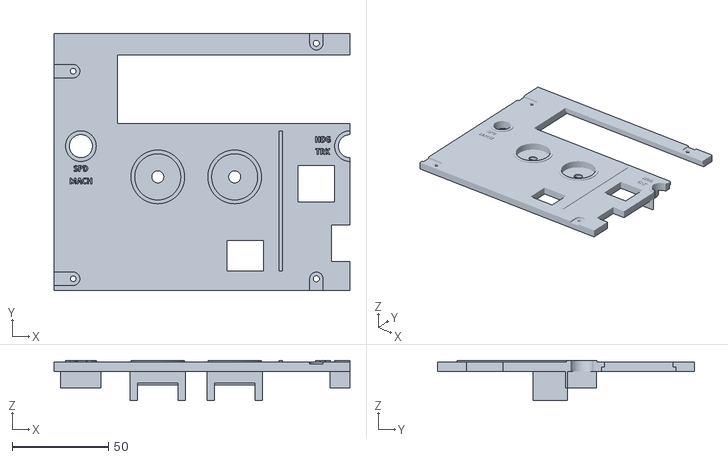
[picture p89: CAD file, 2025-06-19]
STL Files/01_FCU_V4b_LEFT_transparent.stl
154.0 x 133.5 x 20.9
