stefanofinetti/MF_fcu_efis_mainboard/STL Files/FCU_12mm_button_keeper.stl

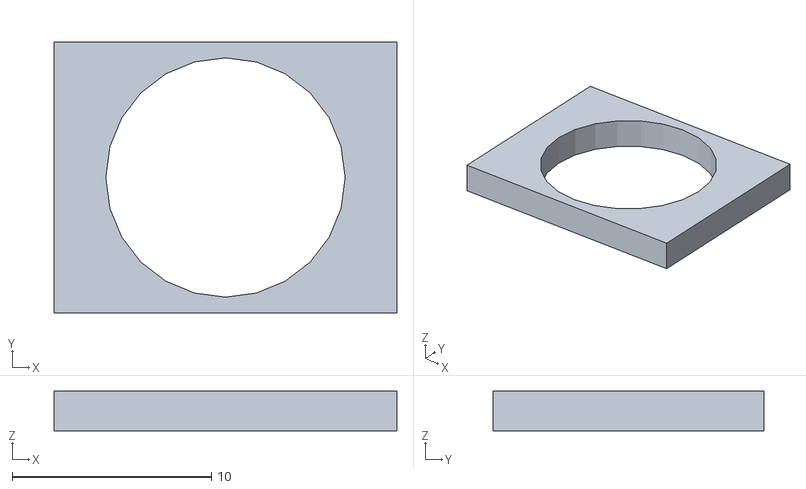
[picture p91: CAD file, 2025-02-01]
STL Files/FCU_12mm_button_keeper.stl
17.2 x 13.6 x 2.00
