stefanofinetti/MF_fcu_efis_mainboard/STL Files/FCU_12mm_button_case.stl

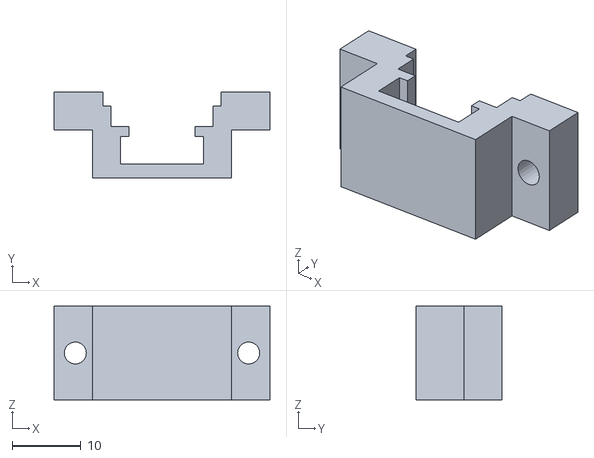
[picture p93: CAD file, 2025-02-01]
STL Files/FCU_12mm_button_case.stl
31.4 x 12.5 x 13.6
