stefanofinetti/MF_fcu_efis_mainboard/STL Files/FCU_V4_OLED_MASK_V4.3mf

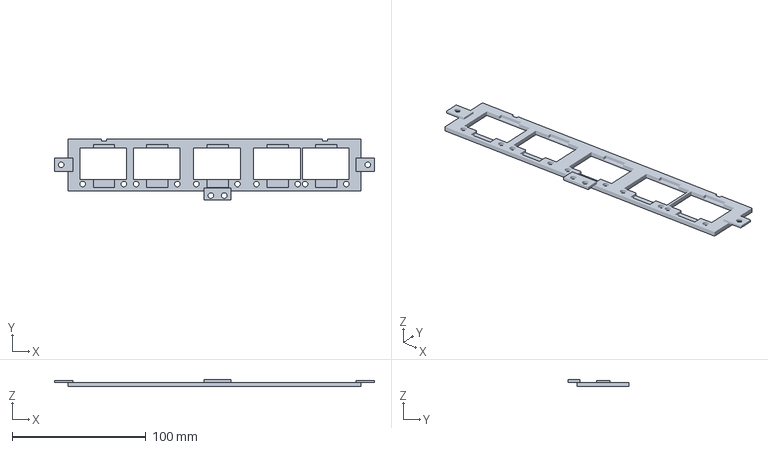
[picture p94: CAD file, 2025-02-01]
STL Files/FCU_V4_OLED_MASK_V4.3mf
239.4 x 46.0 x 5.00 mm
