stefanofinetti/MF_fcu_efis_mainboard/STL Files/Knobs.3mf

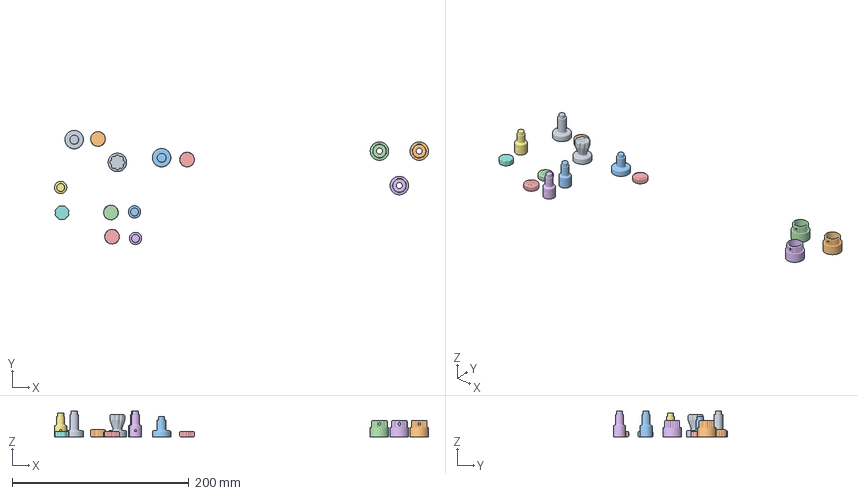
[picture p95: CAD file, 2025-02-01]
STL Files/Knobs.3mf
423.3 x 129.3 x 29.0 mm
HDG Knob ma04-HDG Knob.stl
ALT Knob ma11-ALT Ring.stl x 2
VS Knob ma04-Speed Base.stl
Baro Knob ma11-Baro Ring.stl
VS Knob ma04-Speed Top.stl
ALT Knob ma11-ALT Base.stl
ALT Knob ma11-ALT Top.stl
Speed Knob ma06-Speed Base.stl
Speed Knob ma06-Speed Top.stl
Baro Knob ma11-Baro Base.stl x 2
Baro Knob ma11-Baro Top.stl x 2
