stefanofinetti/MF_fcu_efis_mainboard/STL Files/Rotaries_Buttons.3mf

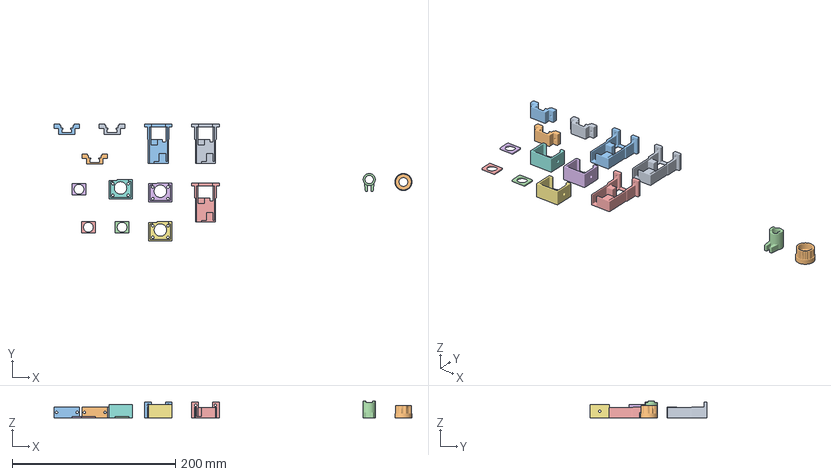
[picture p98: CAD file, 2025-02-01]
STL Files/Rotaries_Buttons.3mf
438.4 x 143.0 x 20.7 mm
SL3 - FCU Push-Pull Rotary Mk3 - Outer.stl x 3
ALT Knob Outer 100-1000 part 4.stl
ALT Knob switch flipper part 4.stl
Alt-baro-Rotary-ConnectionPanel.stl x 3
FCU_12mm_button_case.stl x 3
FCU_12mm_button_keeper.stl x 3
