stefanofinetti/MF_fcu_efis_mainboard/VsCode Files/SF_FCU/MFCustomDevice.h

#pragma once

#include <Arduino.h>
#include "FCU_EFIS.h"

// only one entry required if you have only one custom device
enum {
    FCU_EFIS_DEVICE = 1
};
class MFCustomDevice
{
public:
    MFCustomDevice();
    void attach(uint16_t adrPin, uint16_t adrType, uint16_t adrConfig, bool configFromFlash = false);
    void detach();
    void update();
    void set(int16_t messageID, char *setPoint);

private:
    bool      getStringFromMem(uint16_t addrMem, char *buffer, bool configFromFlash);
    bool      _initialized = false;
    FCU_EFIS *_my_FCU_EFIS;
    uint8_t   _customType = 0;
};
